Eng-Roaa/3-Axis-Robotic-Arm/colored_arm.png

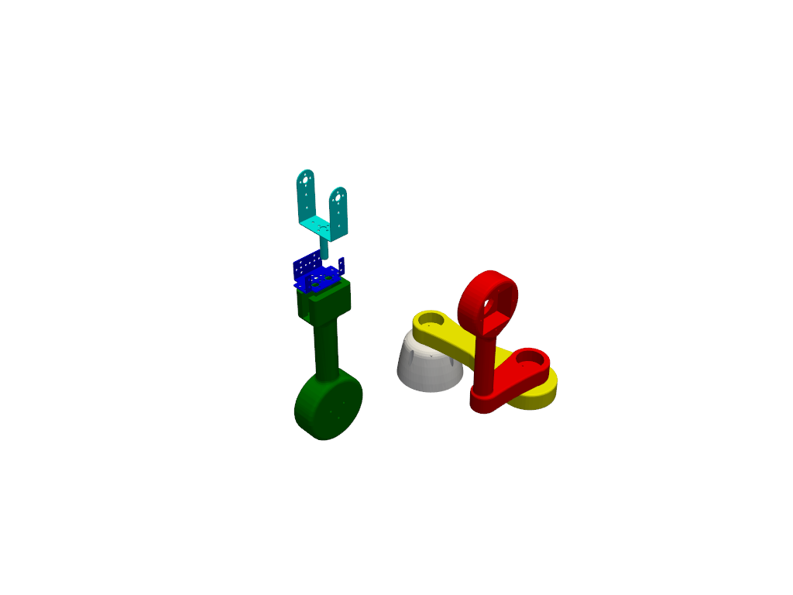
colored_arm.png
