Eng-Roaa/3-Axis-Robotic-Arm/current_arm.png

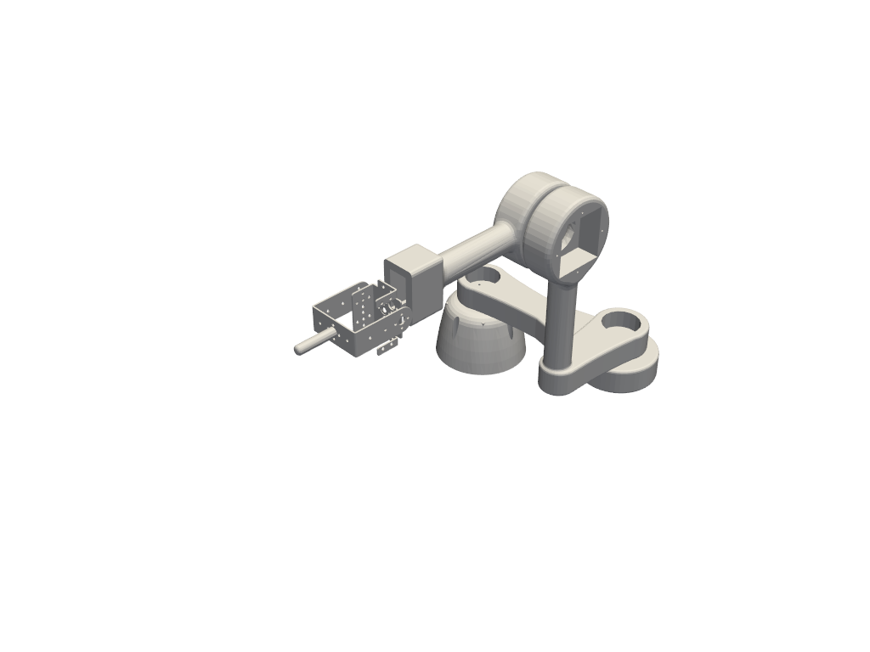
current_arm.png
