Eng-Roaa/3-Axis-Robotic-Arm/Media/WhatsApp Image 2026-09-18 at 6.11.45 PM (1).jpeg

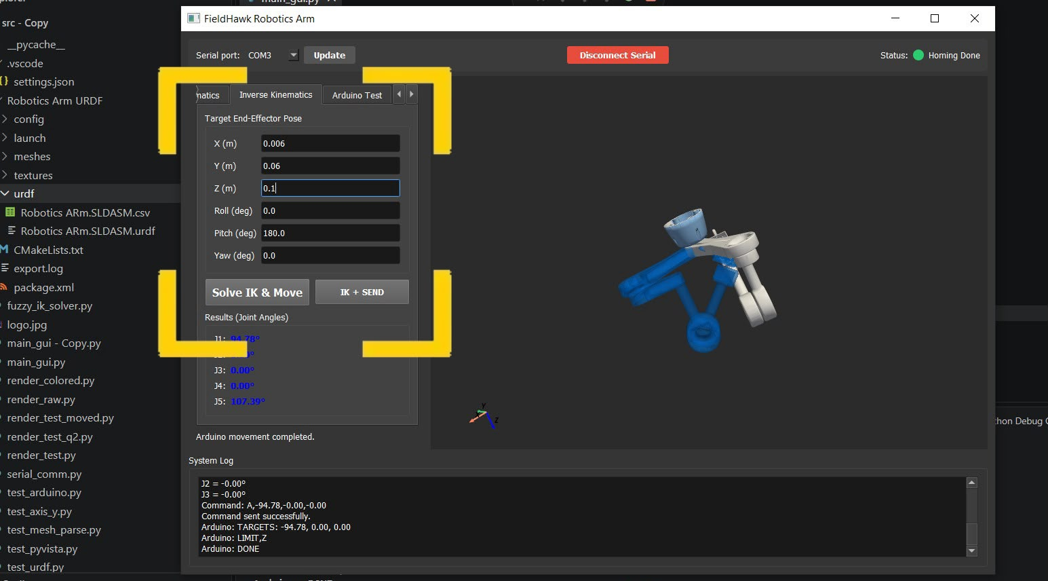
Media/WhatsApp Image 2026-09-18 at 6.11.45 PM (1).jpeg
