Eng-Roaa/3-Axis-Robotic-Arm/moved_arm.png

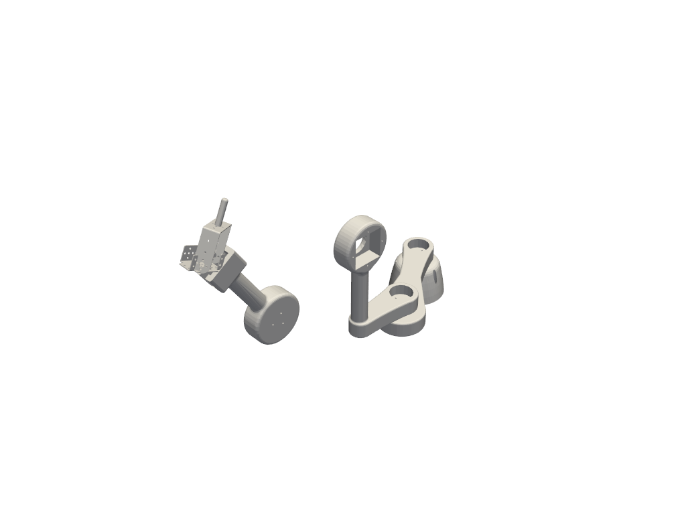
moved_arm.png
