Eng-Roaa/3-Axis-Robotic-Arm/src - Copy/Robotics Arm URDF/meshes/Link_2.STL

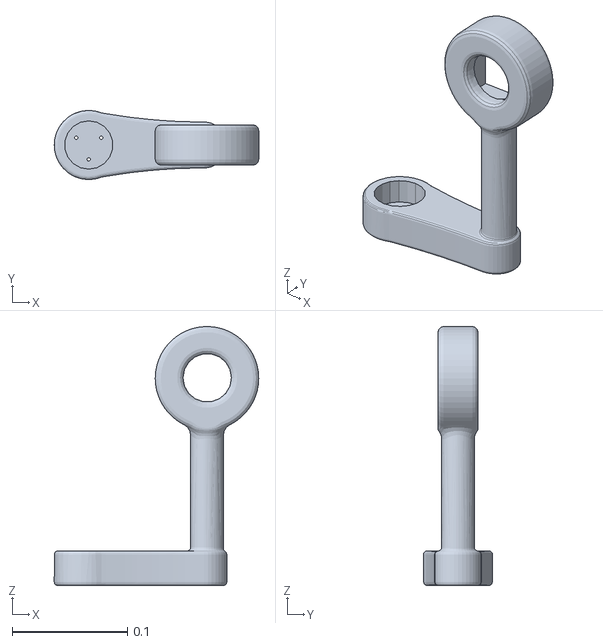
[picture p26: CAD file, 2026-09-18]
src - Copy/Robotics Arm URDF/meshes/Link_2.STL
0.178 x 0.06 x 0.225
