Eng-Roaa/3-Axis-Robotic-Arm/STL Files/Link_One_Base.STL

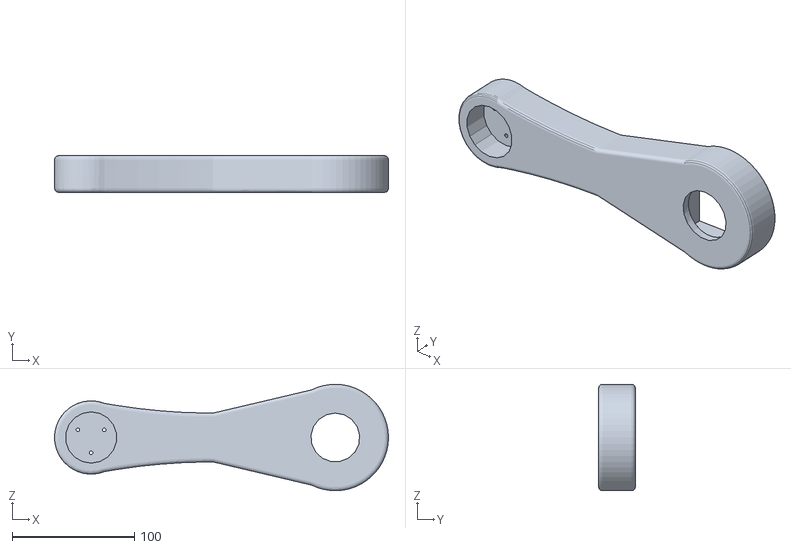
[picture p27: CAD file, 2026-09-18]
STL Files/Link_One_Base.STL
273.6 x 30.0 x 87.1
